M-Skut/kl05z-devboard-demo/media/front-with-kl05.jpg

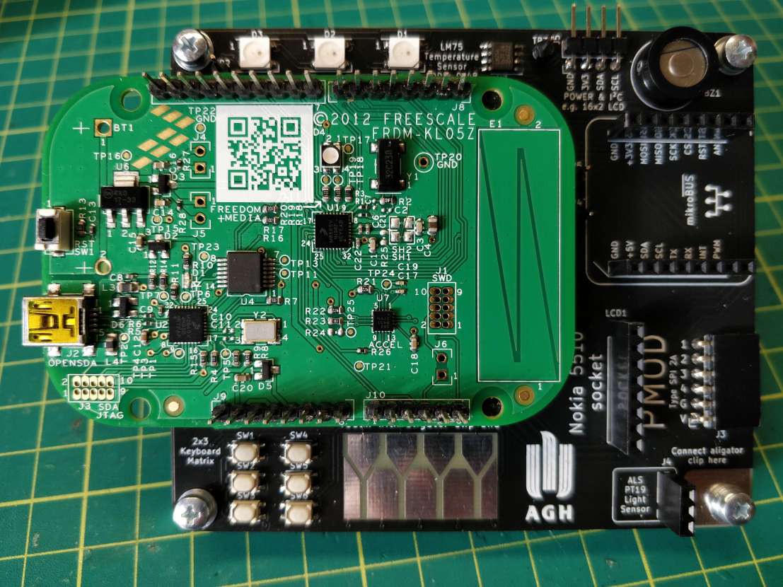
media/front-with-kl05.jpg
