M-Skut/kl05z-devboard-demo/media/rgb_leds.jpg

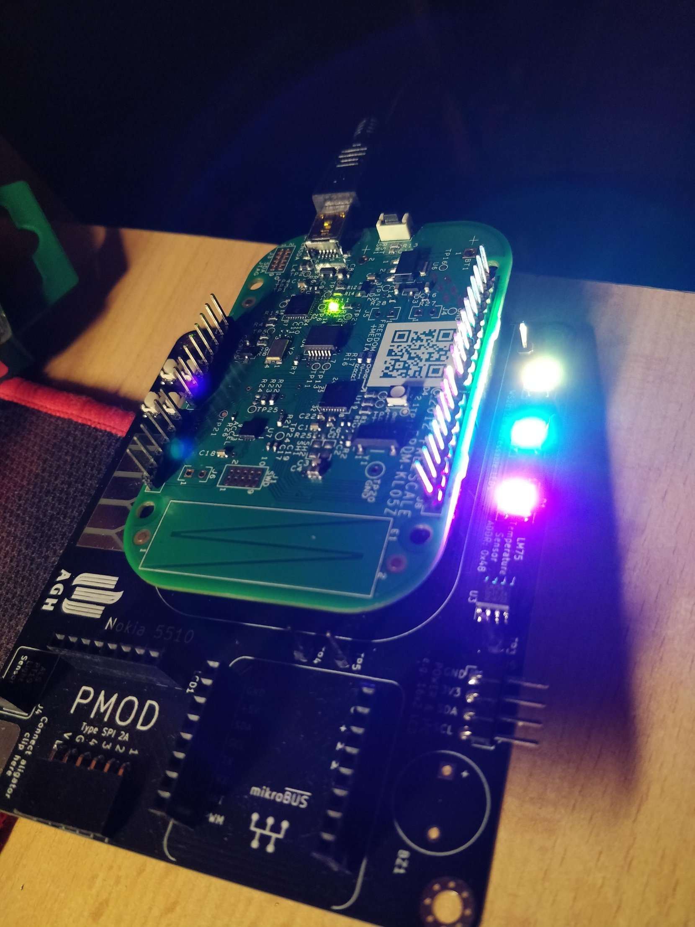
media/rgb_leds.jpg
