M-Skut/kl05z-devboard-demo/device/MKL05Z4/flash_config.c

/******************************************************************************
 * @file     flash_config.c
 * @brief    Flash Configuration Field (FCF) for MKL05Z4
 * @version  V1.0.0
 * @date     20. January 2021
 ******************************************************************************/


#include <stdint.h>

__attribute__ ((section (".cfmconfig"))) const uint8_t _cfm[0x10] = {
   /* NV_BACKKEY3: KEY=0xFF */
    0xFFU,
   /* NV_BACKKEY2: KEY=0xFF */
    0xFFU,
   /* NV_BACKKEY1: KEY=0xFF */
    0xFFU,
   /* NV_BACKKEY0: KEY=0xFF */
    0xFFU,
   /* NV_BACKKEY7: KEY=0xFF */
    0xFFU,
   /* NV_BACKKEY6: KEY=0xFF */
    0xFFU,
   /* NV_BACKKEY5: KEY=0xFF */
    0xFFU,
   /* NV_BACKKEY4: KEY=0xFF */
    0xFFU,
   /* NV_FPROT3: PROT=0xFF */
    0xFFU,
   /* NV_FPROT2: PROT=0xFF */
    0xFFU,
   /* NV_FPROT1: PROT=0xFF */
    0xFFU,
   /* NV_FPROT0: PROT=0xFF */
    0xFFU,
   /* NV_FSEC: KEYEN=1,MEEN=3,FSLACC=3,SEC=2 */
    0x7EU,
   /* NV_FOPT: ??=1,??=1,FAST_INIT=1,LPBOOT1=1,RESET_PIN_CFG=1,NMI_DIS=1,??=1,LPBOOT0=1 */
    0xFFU,
    0xFFU,
    0xFFU
};
